maunope/DifferentiaPressureSensor/src/config_params.h

#ifndef CONFIG_PARAMS_H
#define CONFIG_PARAMS_H

#include <stdint.h>
#include "../lib/i2c_d6fph/i2c_d6fph.h"

/**
 * @brief Structure to hold all runtime configuration parameters.
 */
typedef struct {
    float battery_voltage_divider_ratio;
    /**
     * @brief The minimum battery voltage required to write data to the SD card.
     * This acts as a safety measure to prevent data corruption that can occur
     * if the device loses power during a write operation. If the measured
     * battery voltage is below this threshold, logging to the SD card is suspended.
     */
    float battery_voltage_treshold;
    uint32_t inactivity_timeout_ms;
    uint64_t sleep_duration_ms;
    uint32_t log_interval_ms;
    char wifi_ssid[64];
    char wifi_password[64];
    d6fph_sensor_model_t d6fph_model;
    uint64_t hf_sleep_duration_ms;
    uint32_t hf_log_interval_ms;
    // Kalman filter coefficients
    float kf_temp_q;
    float kf_temp_r;
    float kf_press_q;
    float kf_press_r;
    float kf_diff_press_q;
    float kf_diff_press_r;
    float kf_batt_v_q;
    float kf_batt_v_r;
    // Kalman filter coefficients for High-Frequency mode
    float kf_temp_q_hf;
    float kf_temp_r_hf;
    float kf_press_q_hf;
    float kf_press_r_hf;
    float kf_diff_press_q_hf;
    float kf_diff_press_r_hf;
    float kf_batt_v_q_hf;
    float kf_batt_v_r_hf;
} config_params_t;

/**
 * @brief Initializes the configuration parameters by loading them from NVS.
 *
 * This function should be called once at startup after the config_manager
 * has potentially loaded new values from the SD card.
 */
void config_params_init(void);

/**
 * @brief Gets the version of the currently loaded configuration.
 *
 * @return A version number that changes whenever the config is reloaded.
 */
uint32_t config_get_version(void);

/**
 * @brief Gets a pointer to the global configuration parameters structure.
 *
 * @return A const pointer to the config_params_t structure.
 */
const config_params_t* config_params_get(void);


#endif // CONFIG_PARAMS_H
