maunope/DifferentiaPressureSensor/src/datalogger_task.h

#pragma once

#include "../lib/buffers.h"
#include "freertos/FreeRTOS.h"
#include "freertos/queue.h"
#include "../lib/i2c_bmp280/i2c_bmp280.h"
#include "../lib/i2c_d6fph/i2c_d6fph.h"

// --- Datalogger command queue ---
typedef enum {
    DATALOGGER_CMD_NONE,
    DATALOGGER_CMD_FORCE_REFRESH, // For a full sensor refresh
    DATALOGGER_CMD_REFRESH_BATTERY, // For a battery-only refresh
    DATALOGGER_CMD_PAUSE_WRITES,
    DATALOGGER_CMD_ROTATE_FILE,
    DATALOGGER_CMD_DELETE_FILE,
    DATALOGGER_CMD_SET_MODE,
} datalogger_command_t;

typedef struct {
    datalogger_command_t cmd;
    datalogger_mode_t mode; // Payload for SET_MODE
} datalogger_cmd_msg_t;

extern QueueHandle_t g_datalogger_cmd_queue; // Now a queue of datalogger_cmd_msg_t

typedef struct {
    bmp280_t *bmp280_dev;
    d6fph_t *d6fph_dev;
    uint32_t log_interval_ms;
    uint32_t hf_log_interval_ms;
    bool bmp280_available;
    bool d6fph_available;
} datalogger_task_params_t;

/**
 * @brief Task responsible for periodically reading sensor data and logging it to the SD card.
 *
 * @param pvParameters A pointer to an initialized datalogger_task_params_t struct.
 */
void datalogger_task(void *pvParameters);
